PepVentura/Prisma/stl/tapa_camara_corredera_v0_2.stl

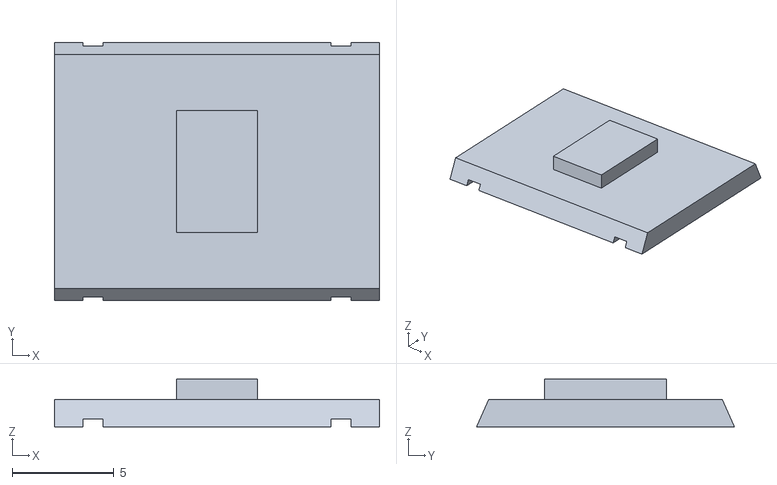
[picture p30: CAD file, 2026-10-03]
stl/tapa_camara_corredera_v0_2.stl
16.0 x 12.7 x 2.35
