PepVentura/Prisma/stl/tapa_camara_prueba_v0_1.stl

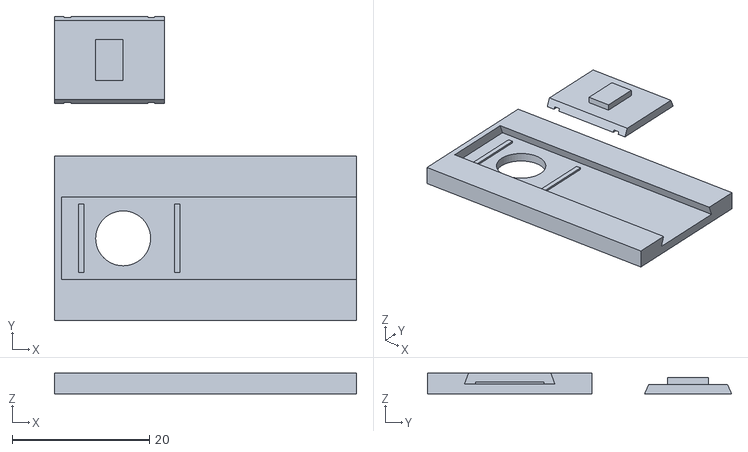
[picture p31: CAD file, 2026-09-30]
stl/tapa_camara_prueba_v0_1.stl
44.0 x 44.4 x 3.00
