PepVentura/Prisma/stl/marco_pantalla_prueba_v0_1.stl

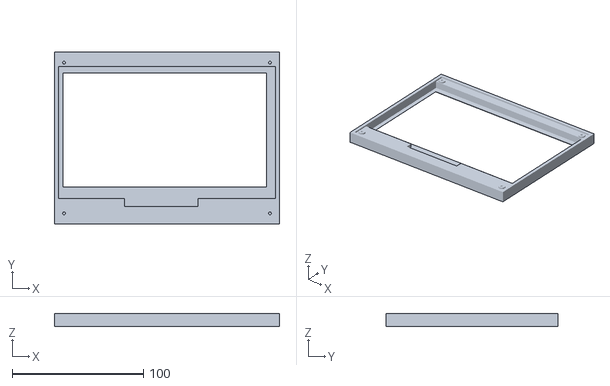
[picture p32: CAD file, 2026-09-30]
stl/marco_pantalla_prueba_v0_1.stl
171.5 x 130.9 x 9.90
